bwickenden/PROJ325/Log book Pages/1.jpg

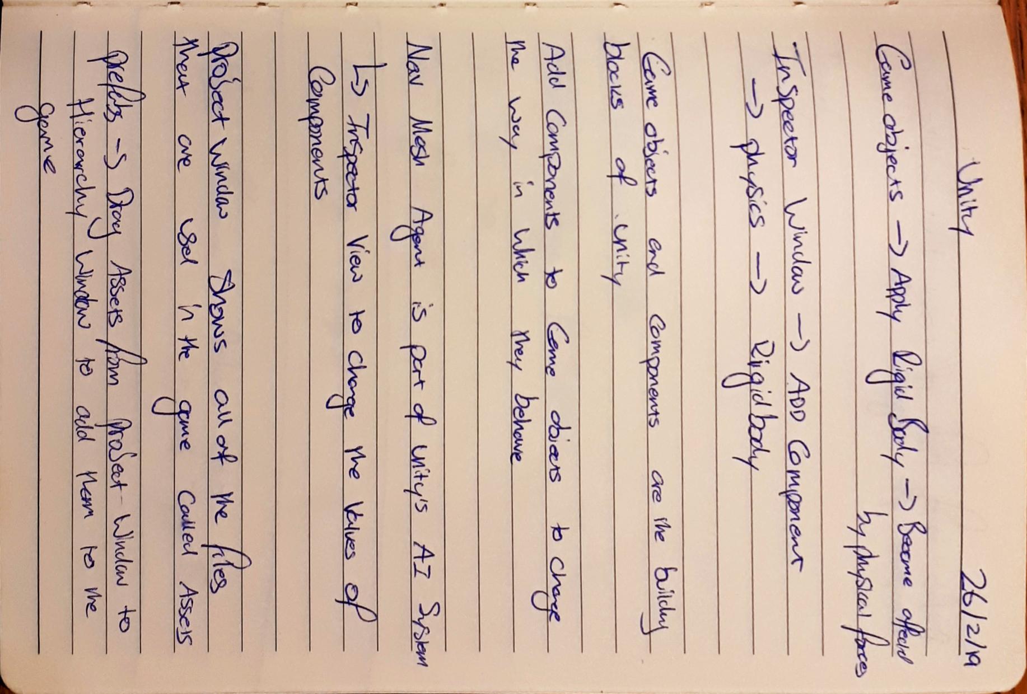
Log book Pages/1.jpg
