bwickenden/PROJ325/Log book Pages/2.jpg

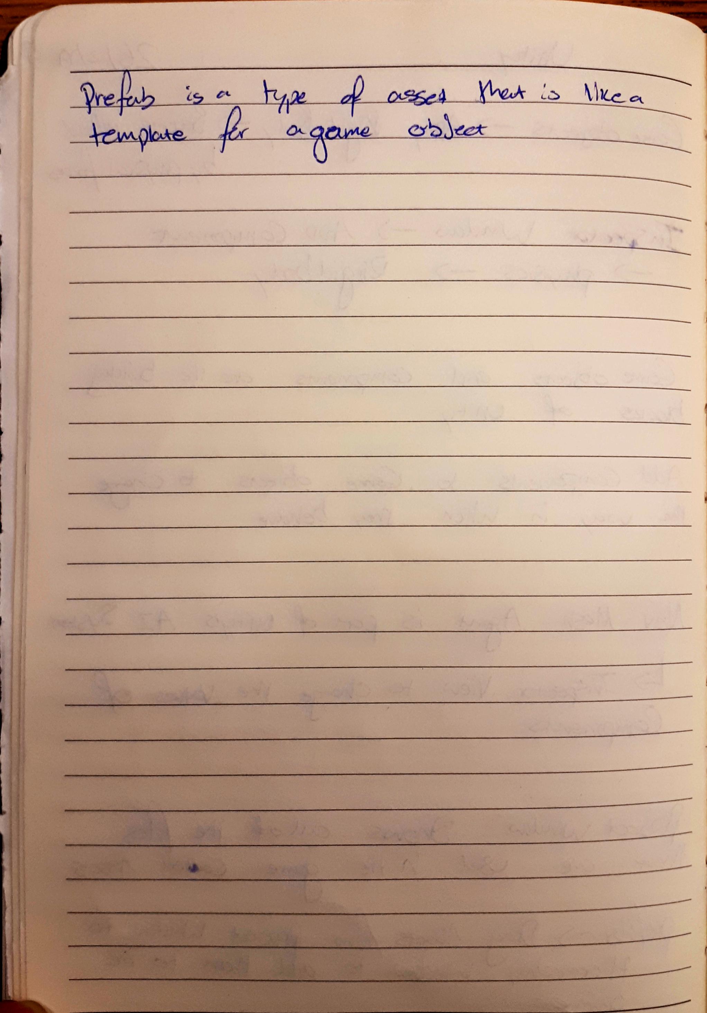
Log book Pages/2.jpg
