bwickenden/PROJ325/Log book Pages/3.jpg

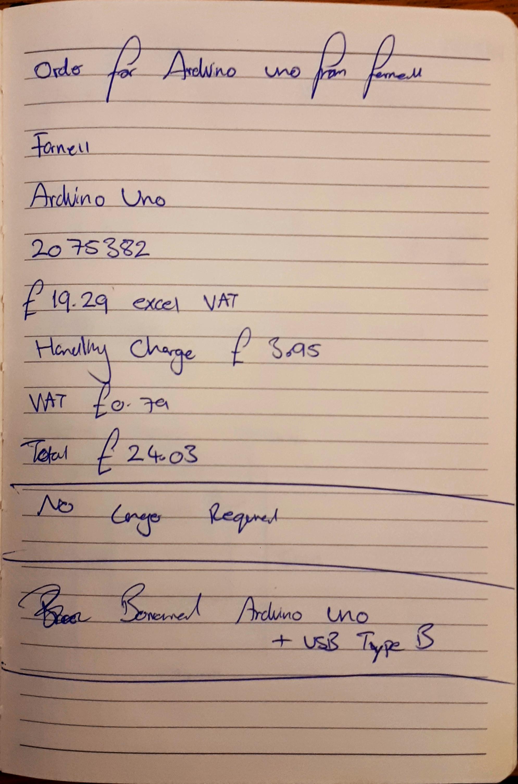
Log book Pages/3.jpg
