bwickenden/PROJ325/Log book Pages/4.jpg

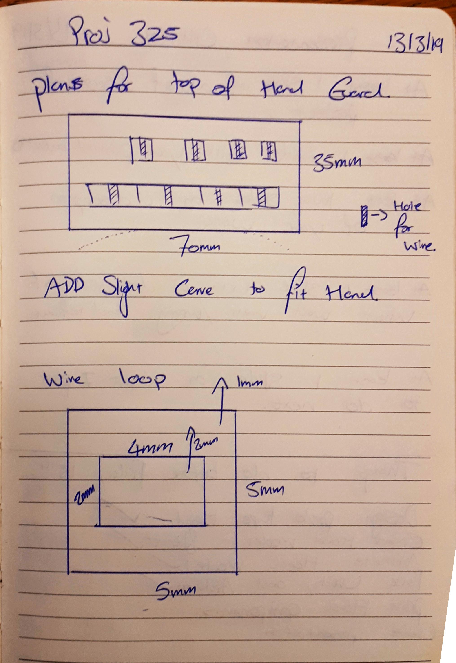
Log book Pages/4.jpg
