bwickenden/PROJ325/Log book Pages/5.jpg

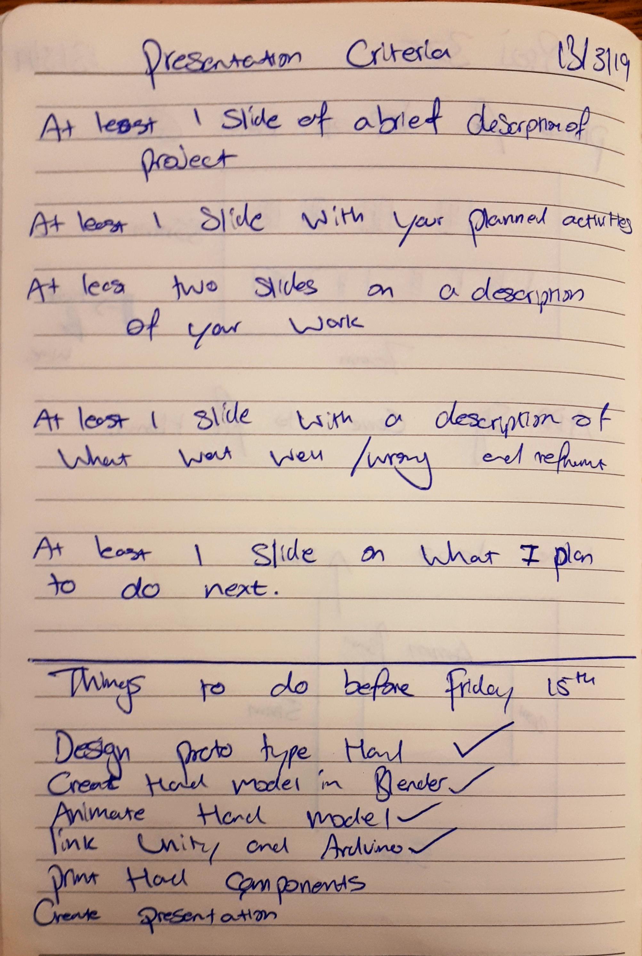
Log book Pages/5.jpg
