bwickenden/PROJ325/Log book Pages/6.jpg

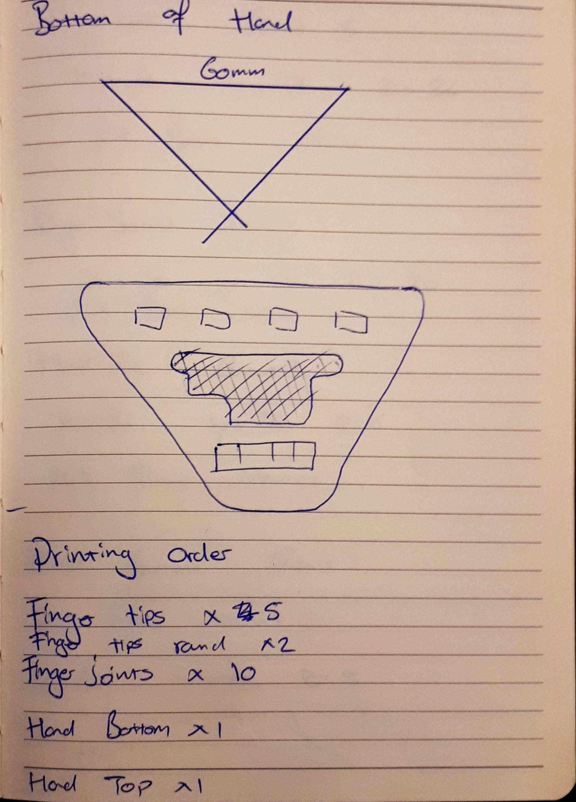
Log book Pages/6.jpg
