bwickenden/PROJ325/Log book Pages/7.jpg

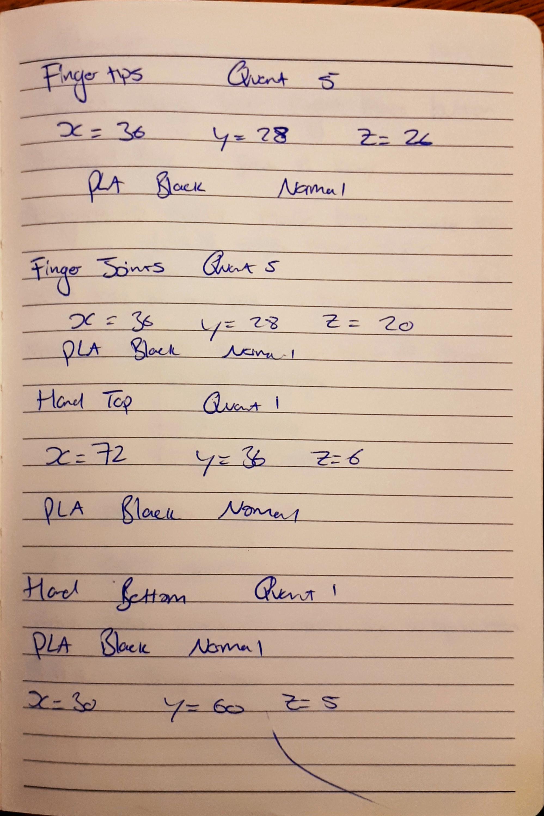
Log book Pages/7.jpg
