bwickenden/PROJ325/Log book Pages/8.jpg

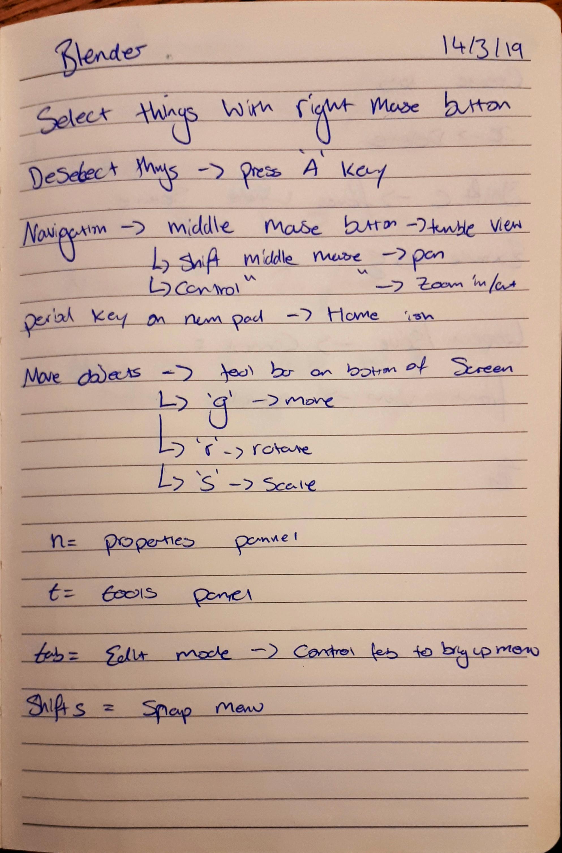
Log book Pages/8.jpg
