bwickenden/PROJ325/Log book Pages/9.jpg

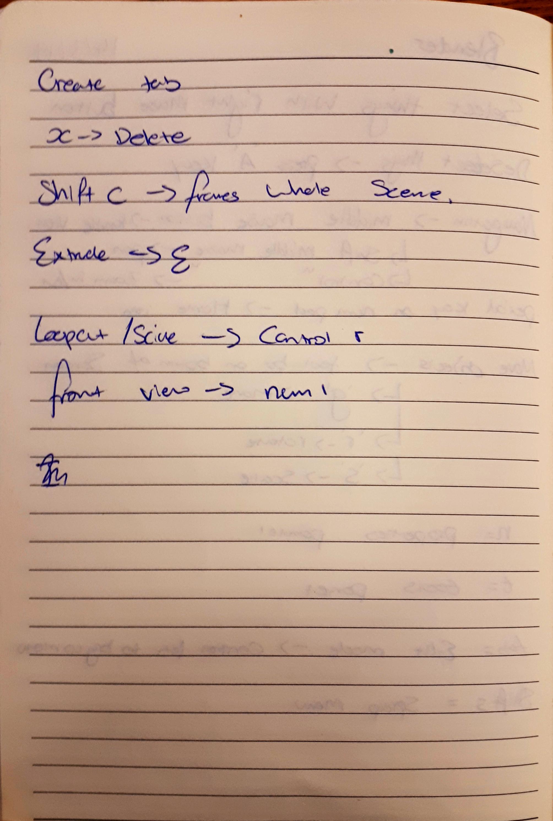
Log book Pages/9.jpg
