bwickenden/PROJ325/Log book Pages/10.jpg

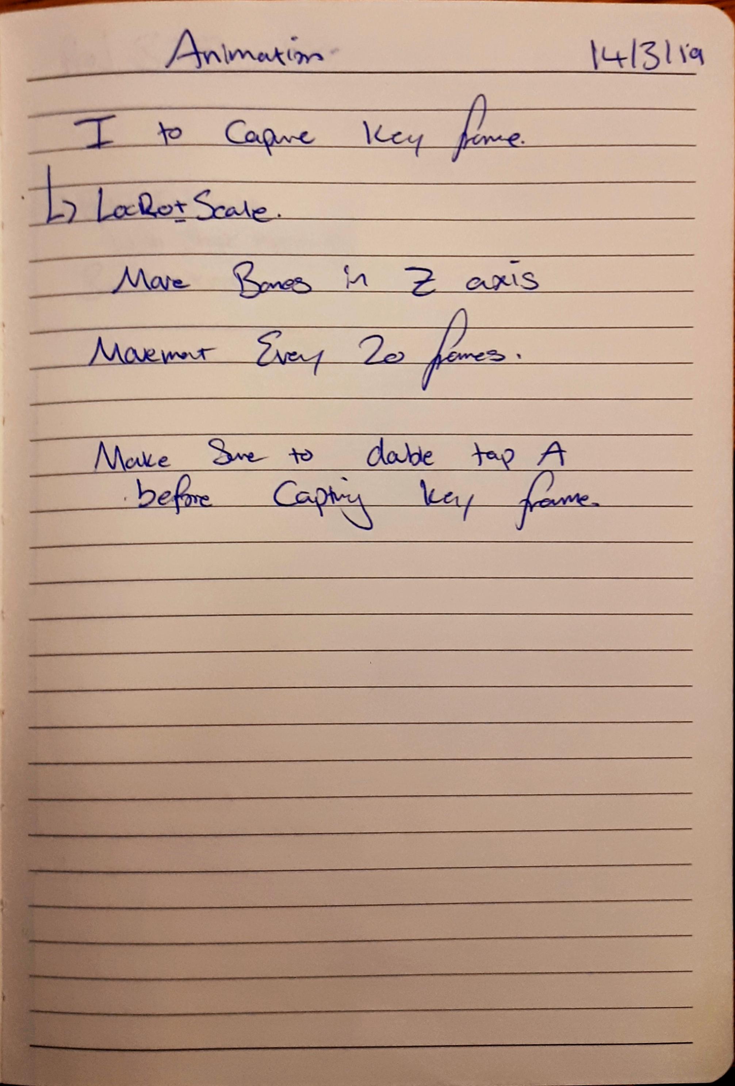
Log book Pages/10.jpg
