bwickenden/PROJ325/Log book Pages/12.jpg

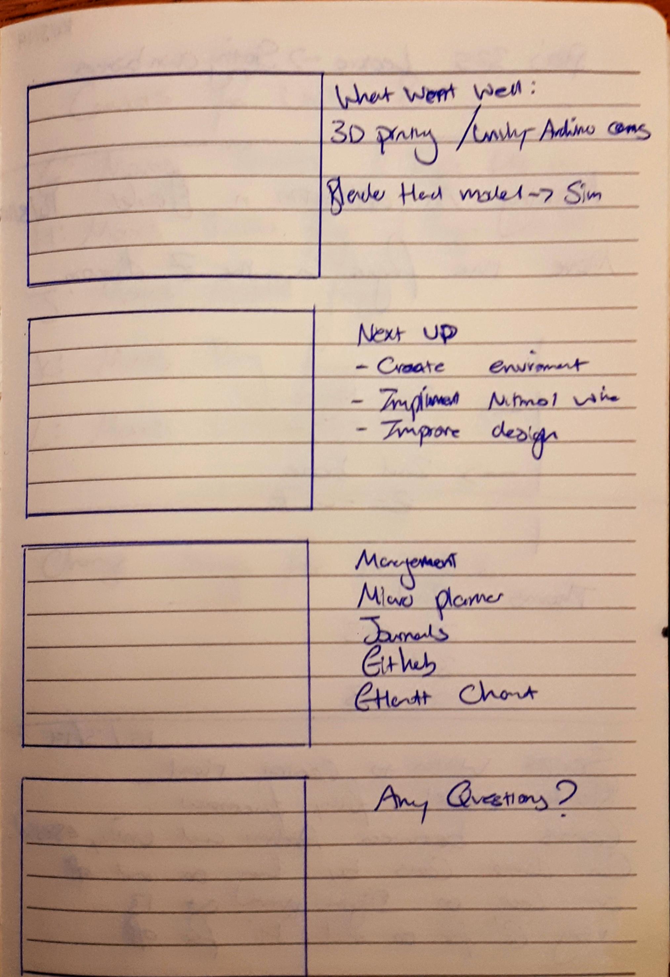
Log book Pages/12.jpg
