bwickenden/PROJ325/Log book Pages/13.jpg

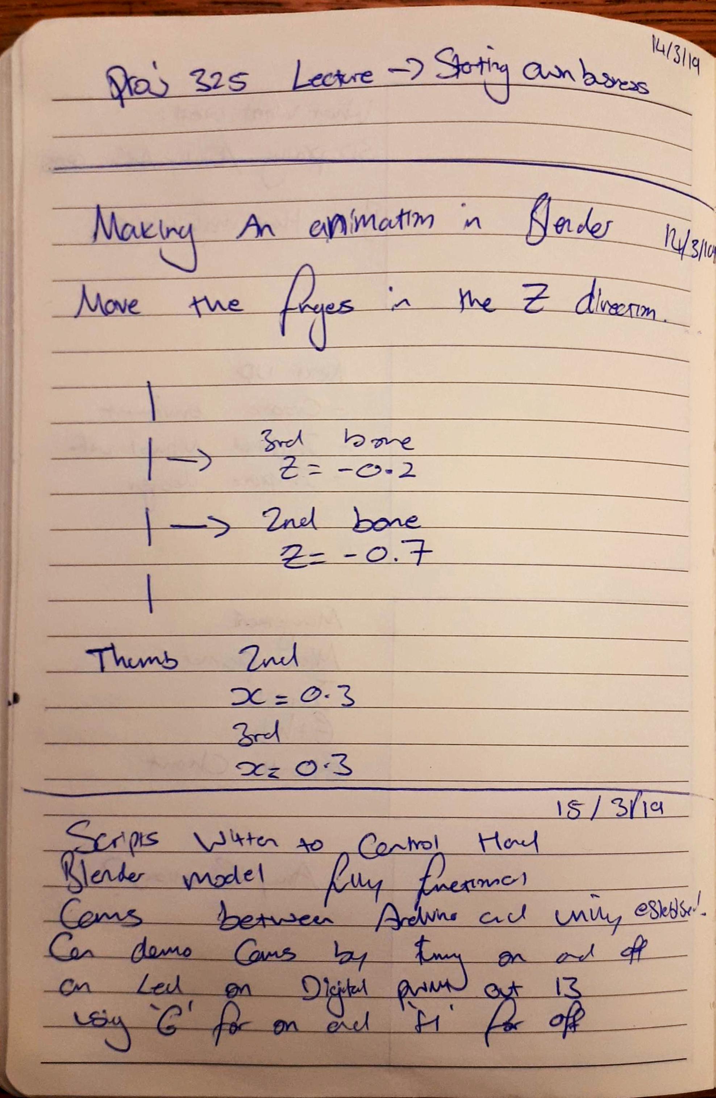
Log book Pages/13.jpg
