bwickenden/PROJ325/Log book Pages/14.jpg

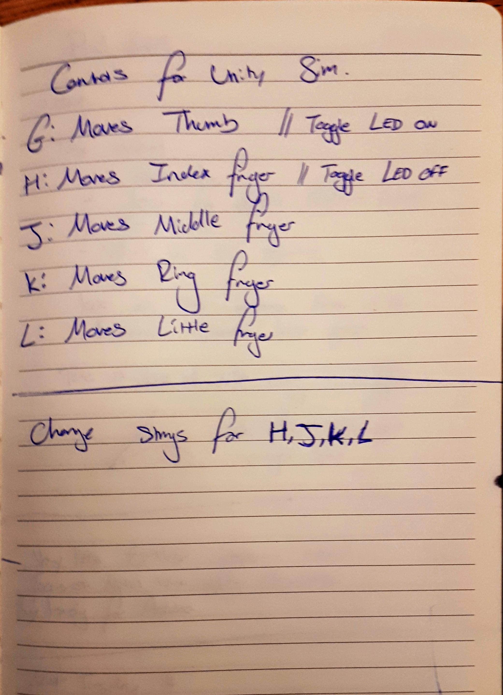
Log book Pages/14.jpg
