bwickenden/PROJ325/Log book Pages/15 (1).jpg

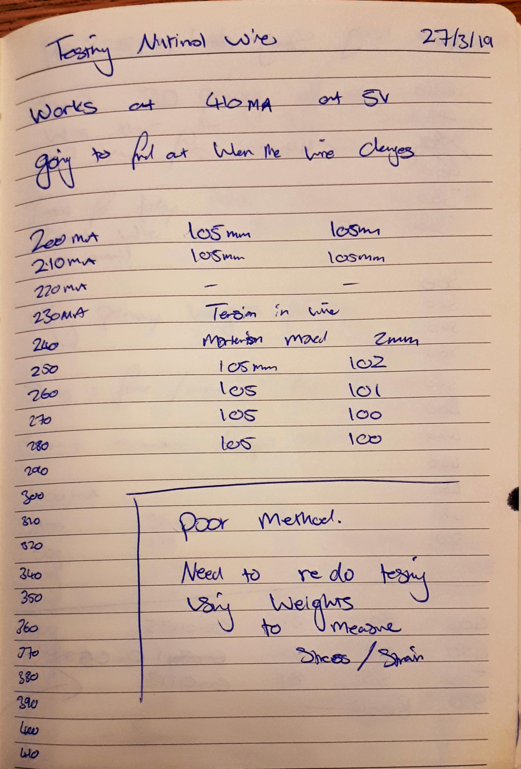
Log book Pages/15 (1).jpg
