bwickenden/PROJ325/Log book Pages/15.jpg

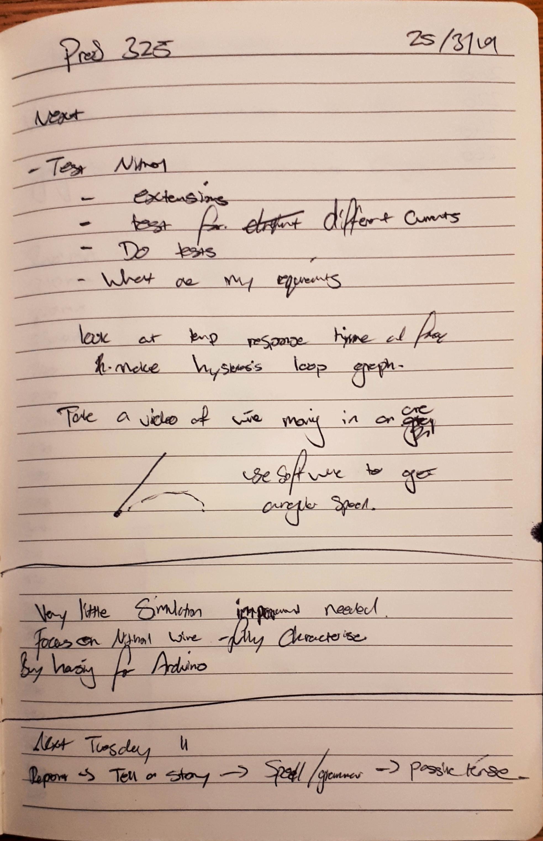
Log book Pages/15.jpg
