bwickenden/PROJ325/Log book Pages/16.jpg

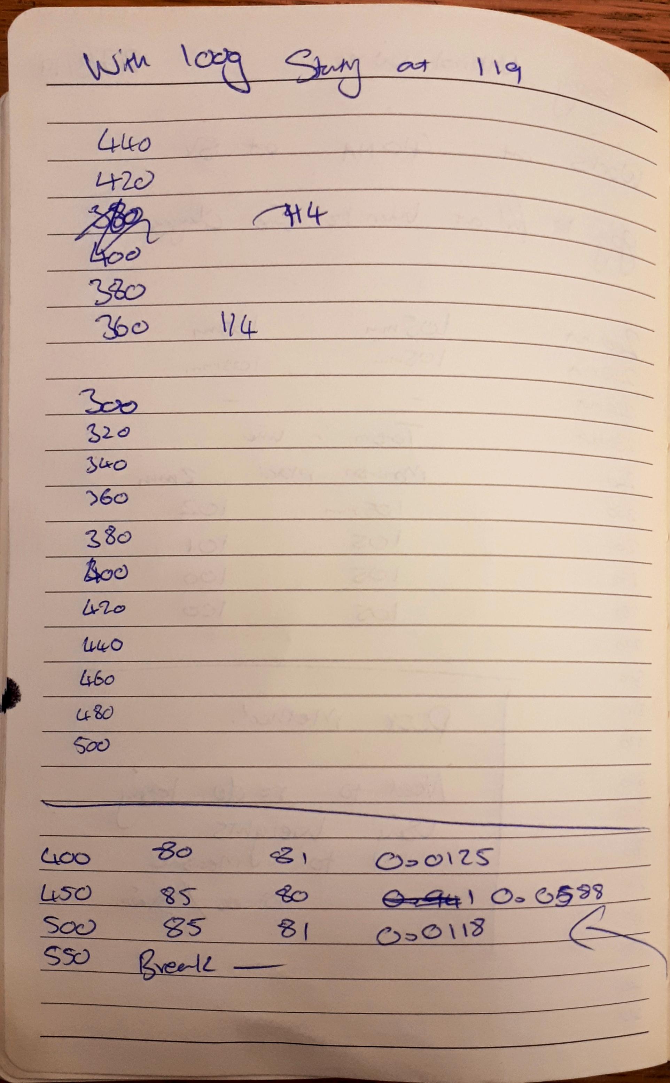
Log book Pages/16.jpg
