bwickenden/PROJ325/Log book Pages/17.jpg

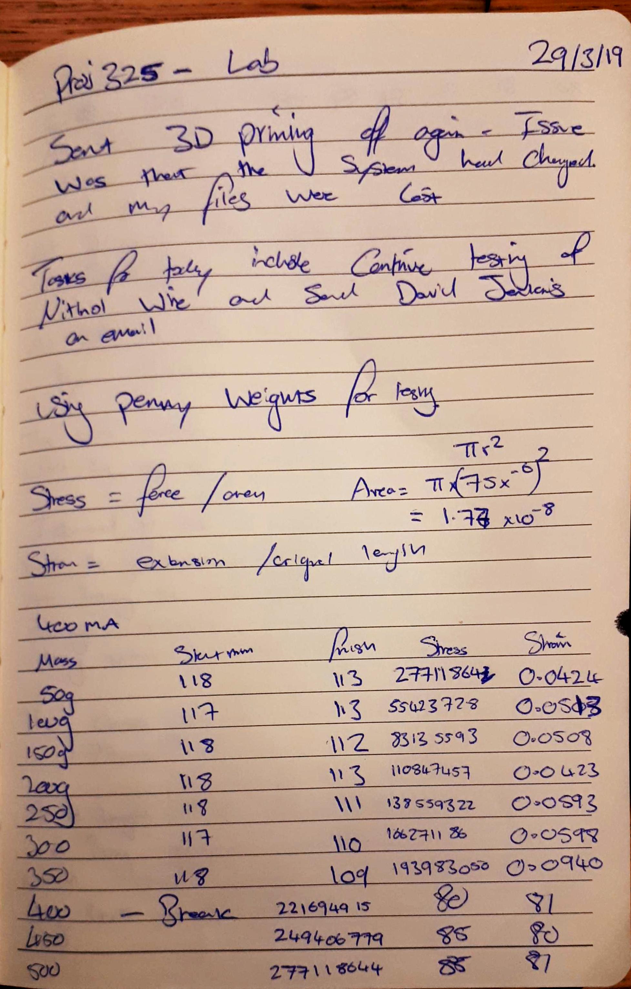
Log book Pages/17.jpg
