bwickenden/PROJ325/Log book Pages/18.jpg

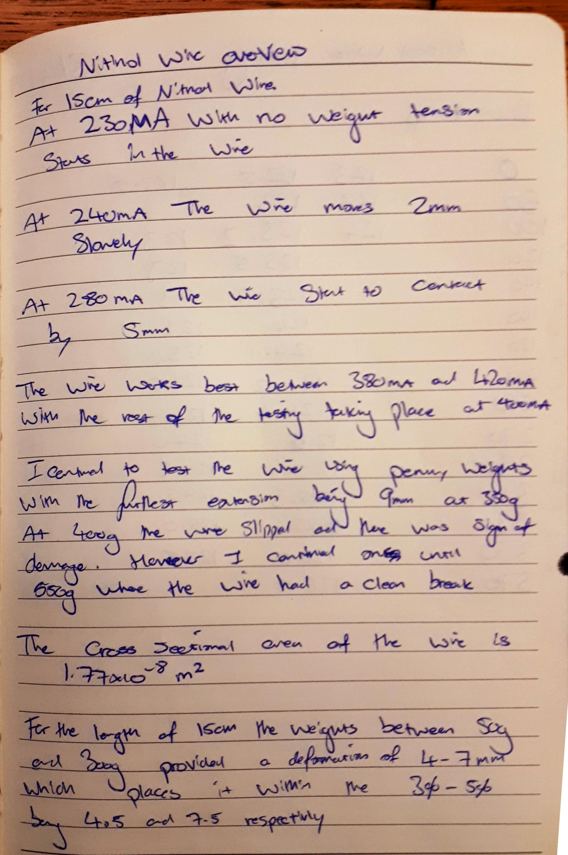
Log book Pages/18.jpg
