bwickenden/PROJ325/Log book Pages/19 (1).jpg

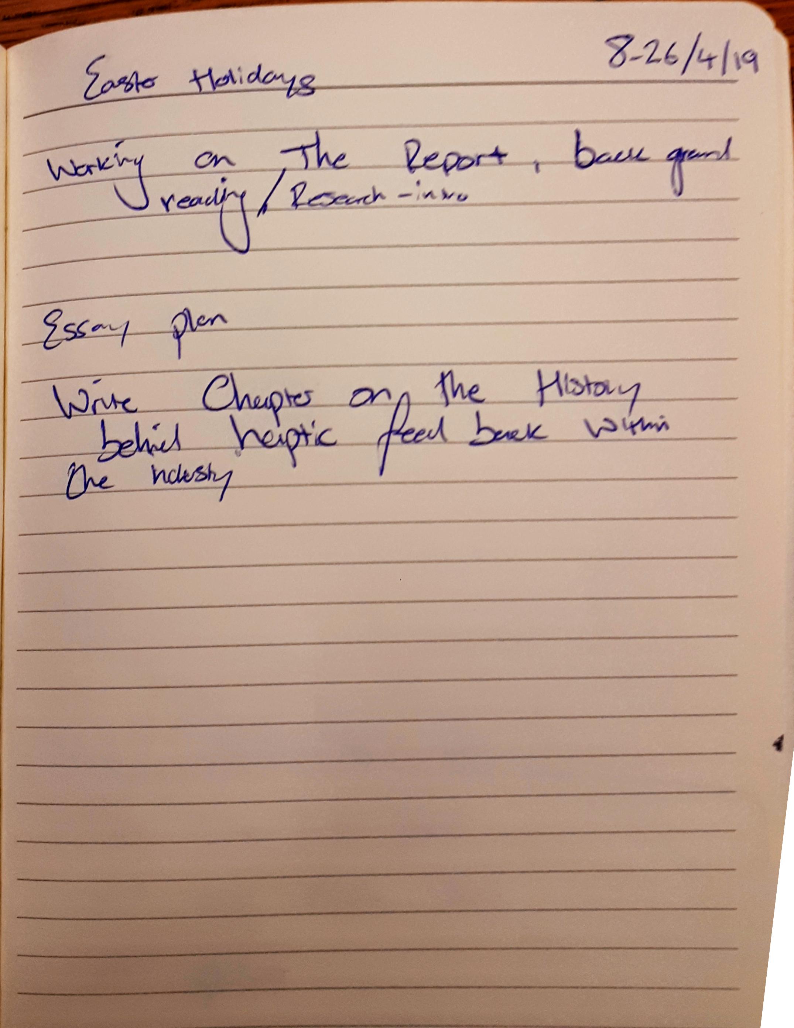
Log book Pages/19 (1).jpg
