bwickenden/PROJ325/Log book Pages/19 (2).jpg

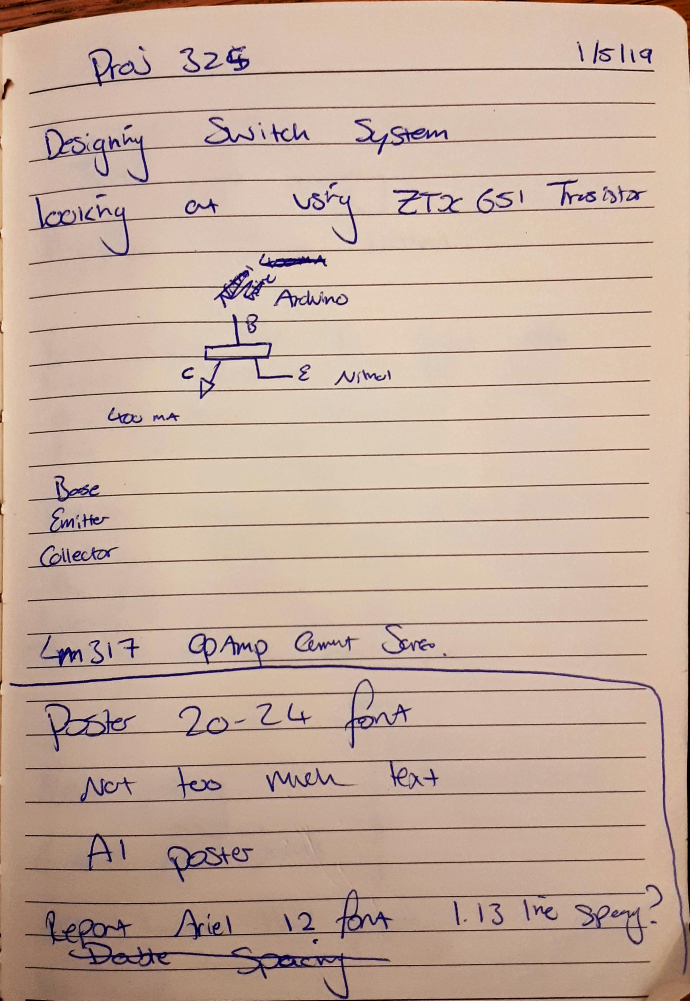
Log book Pages/19 (2).jpg
