bwickenden/PROJ325/Log book Pages/19.jpg

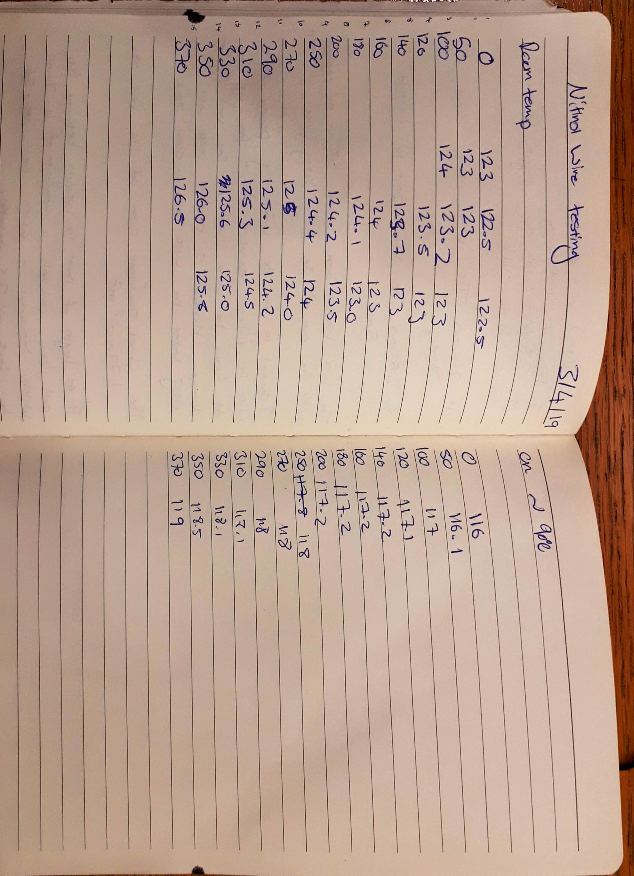
Log book Pages/19.jpg
