bwickenden/PROJ325/Log book Pages/20.jpg

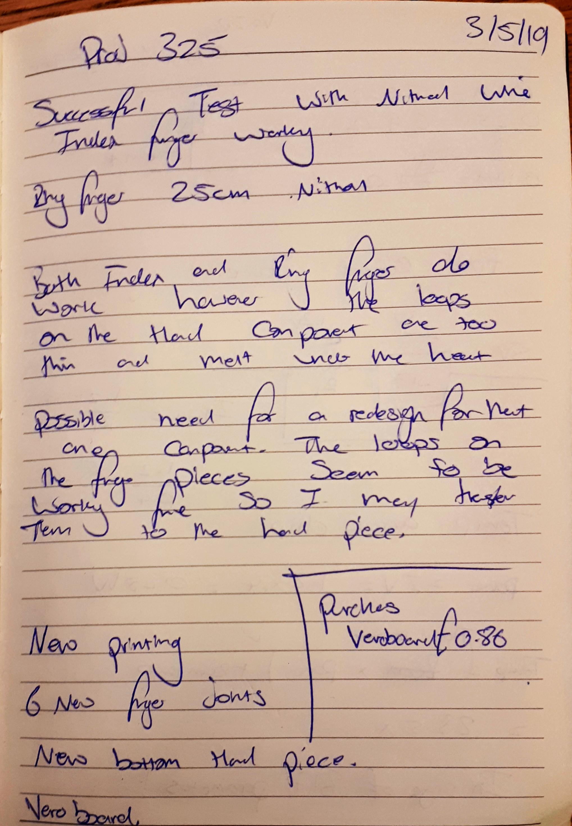
Log book Pages/20.jpg
