bwickenden/PROJ325/Log book Pages/21.jpg

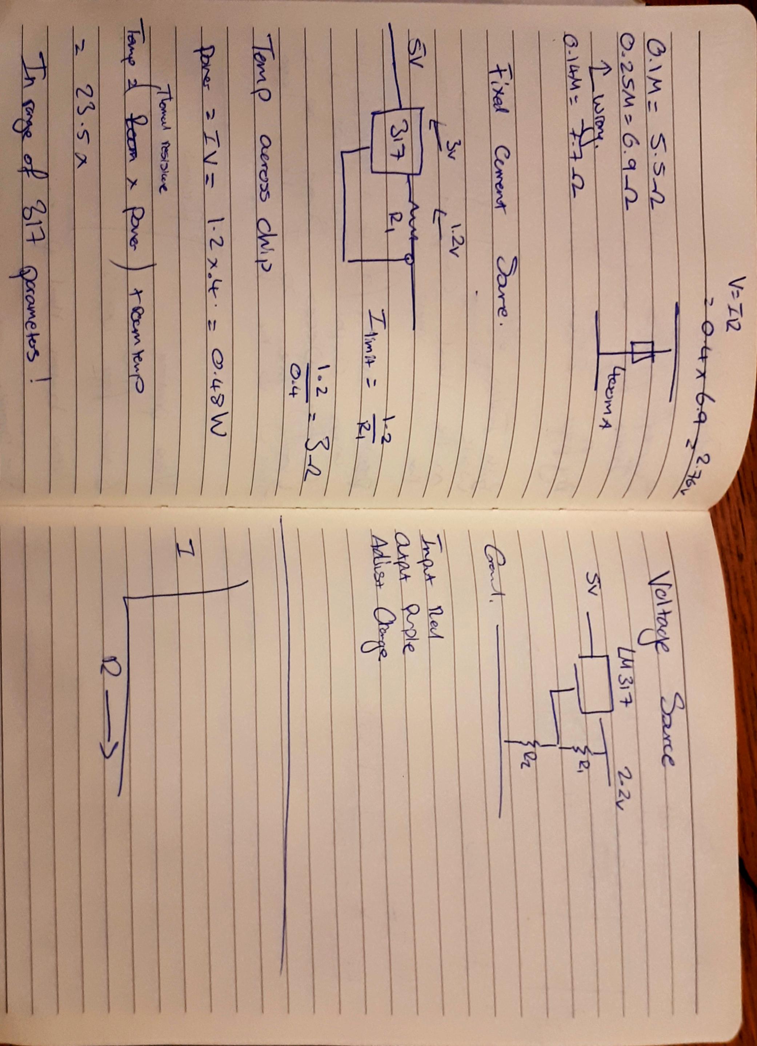
Log book Pages/21.jpg
