bwickenden/PROJ325/Log book Pages/22.jpg

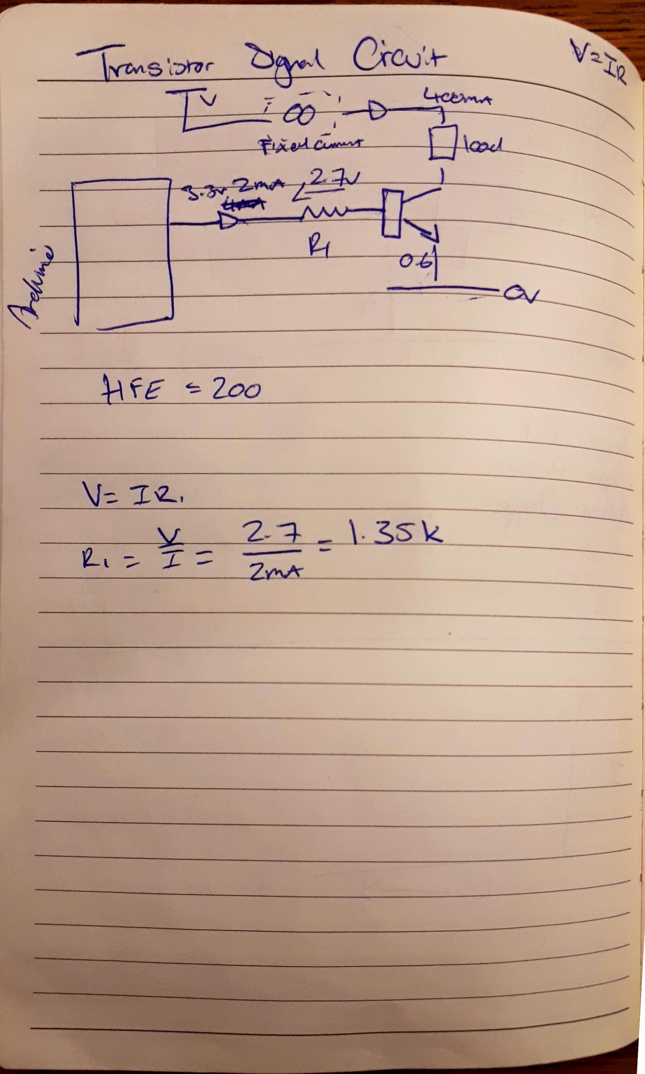
Log book Pages/22.jpg
