bwickenden/PROJ325/Log book Pages/23.jpg

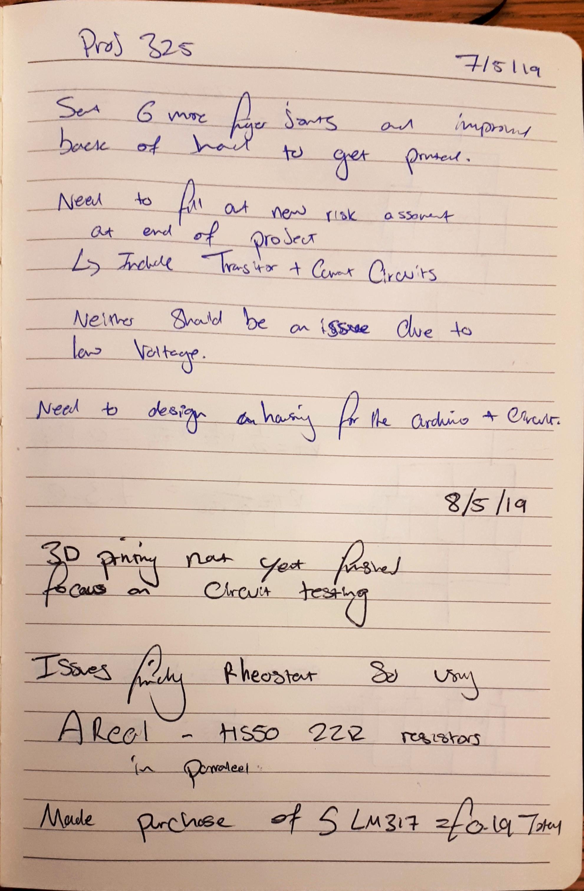
Log book Pages/23.jpg
