bwickenden/PROJ325/Log book Pages/24 (1).jpg

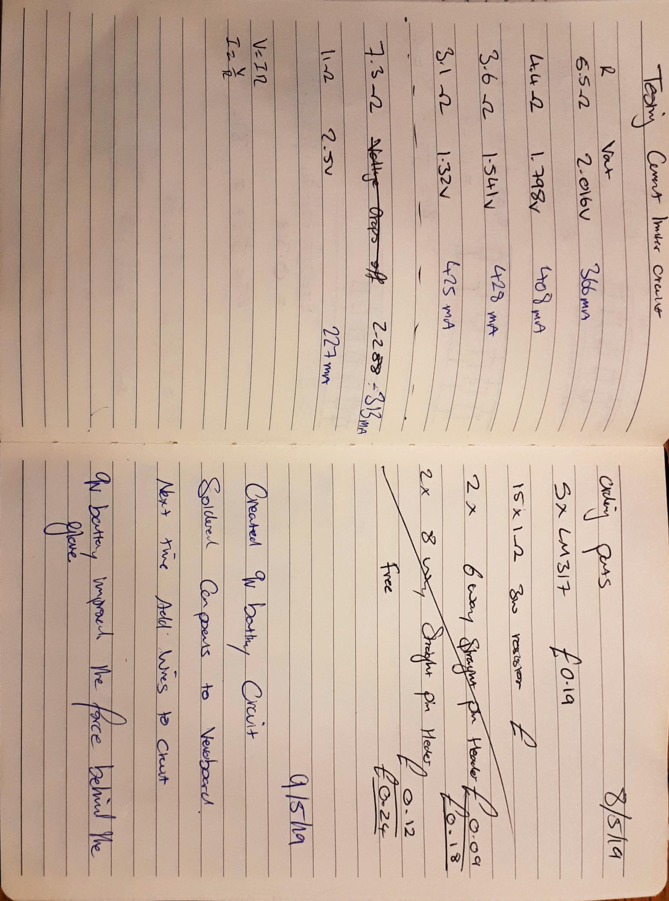
Log book Pages/24 (1).jpg
