bwickenden/PROJ325/Log book Pages/24.jpg

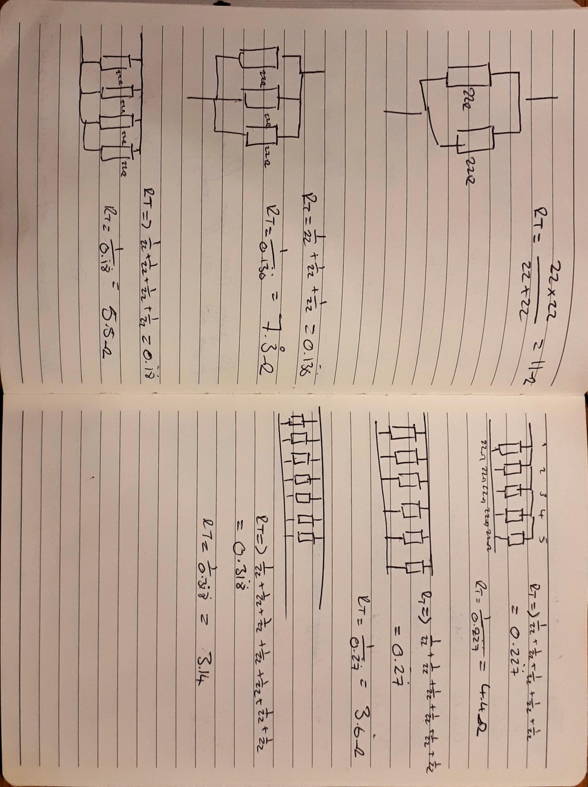
Log book Pages/24.jpg
