bwickenden/PROJ325/Log book Pages/25.jpg

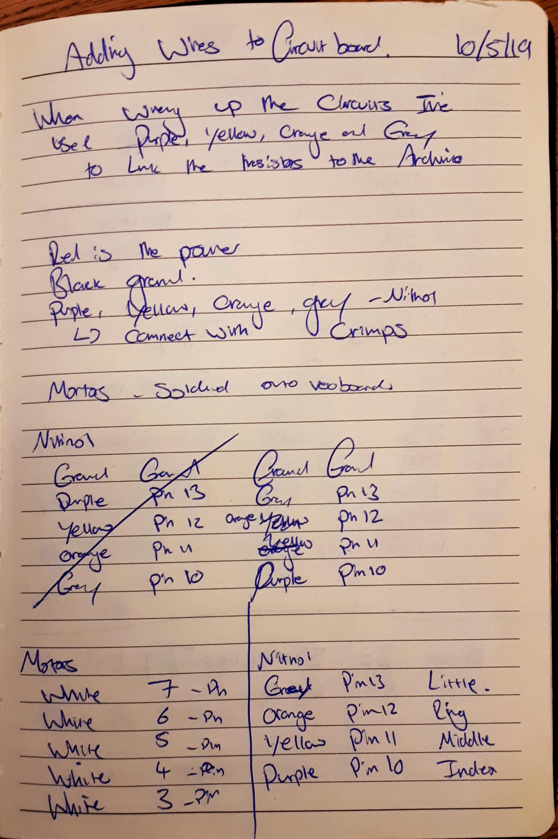
Log book Pages/25.jpg
