bwickenden/PROJ325/Log book Pages/26.jpg

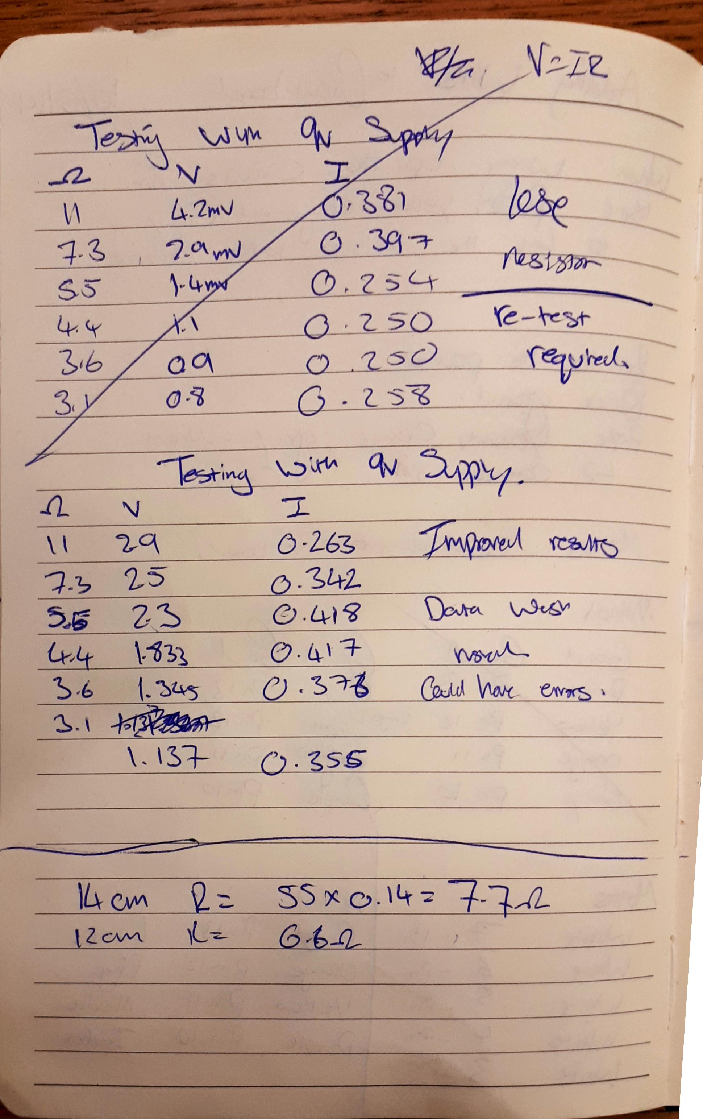
Log book Pages/26.jpg
