bwickenden/PROJ325/Log book Pages/28.jpg

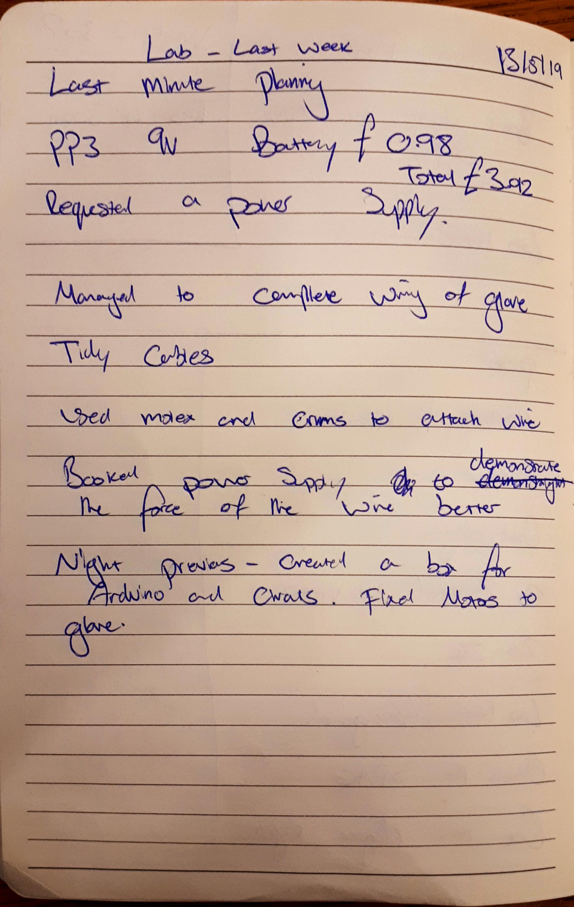
Log book Pages/28.jpg
