bwickenden/PROJ325/Log book Pages/29.jpg

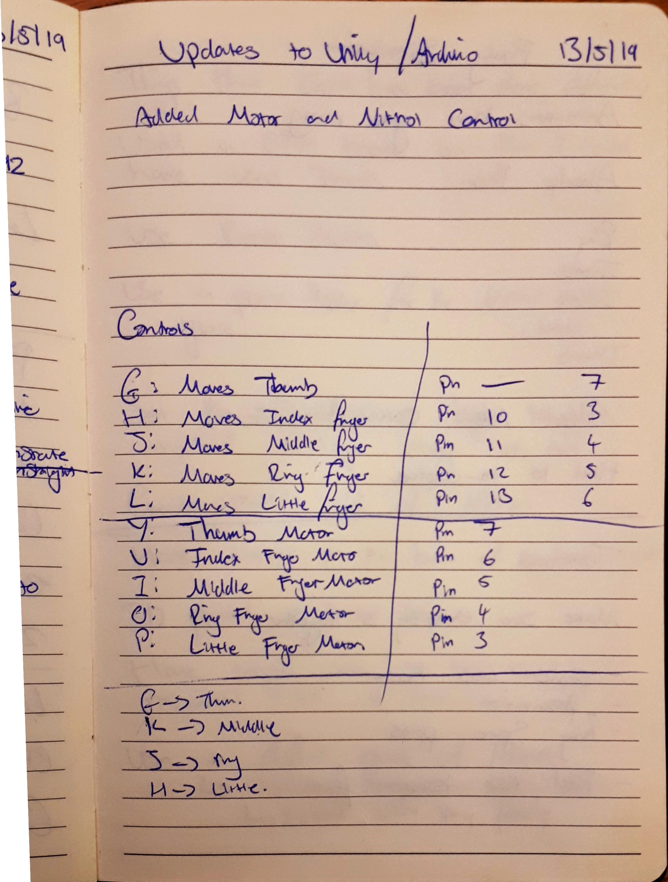
Log book Pages/29.jpg
