bwickenden/PROJ325/Log book Pages/30.jpg

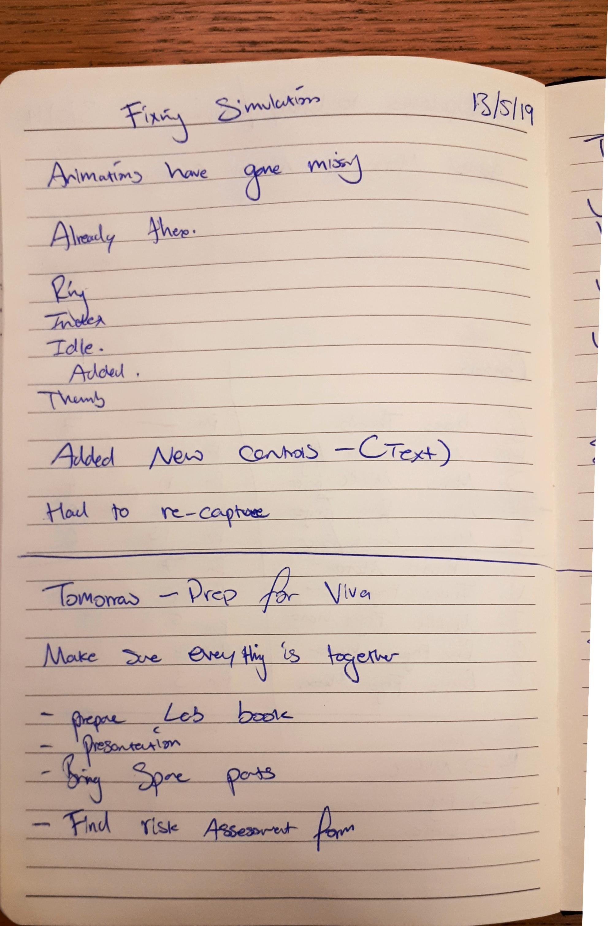
Log book Pages/30.jpg
