bwickenden/PROJ325/Log book Pages/31.jpg

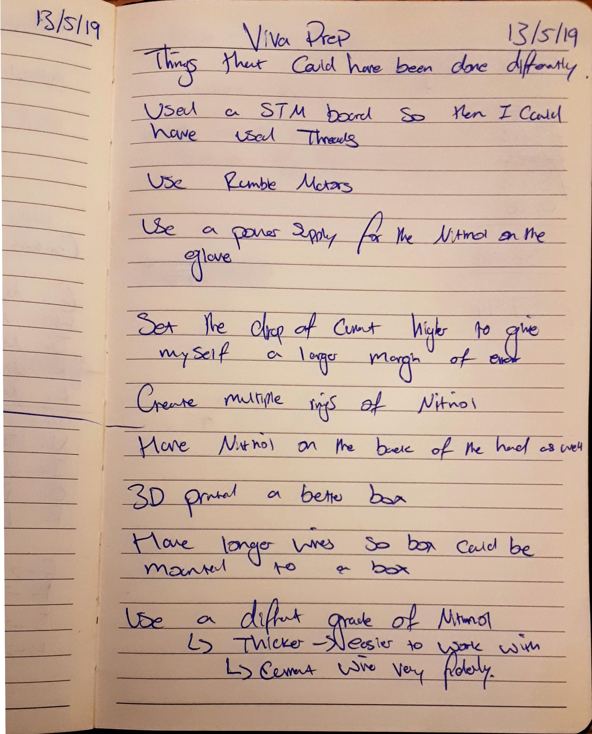
Log book Pages/31.jpg
