bwickenden/PROJ325/Log book Pages/32.jpg

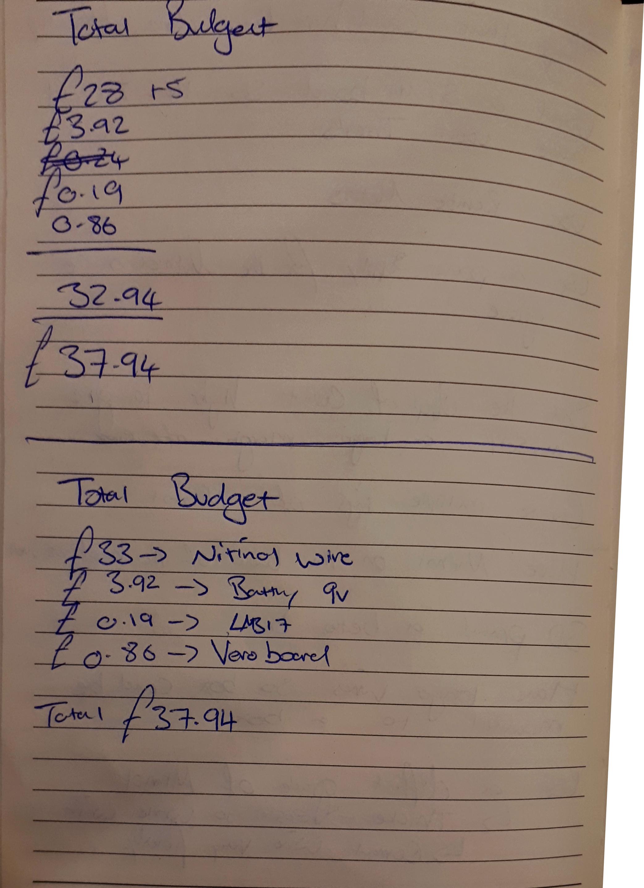
Log book Pages/32.jpg
