bwickenden/PROJ325/Log book Pages/33.jpg

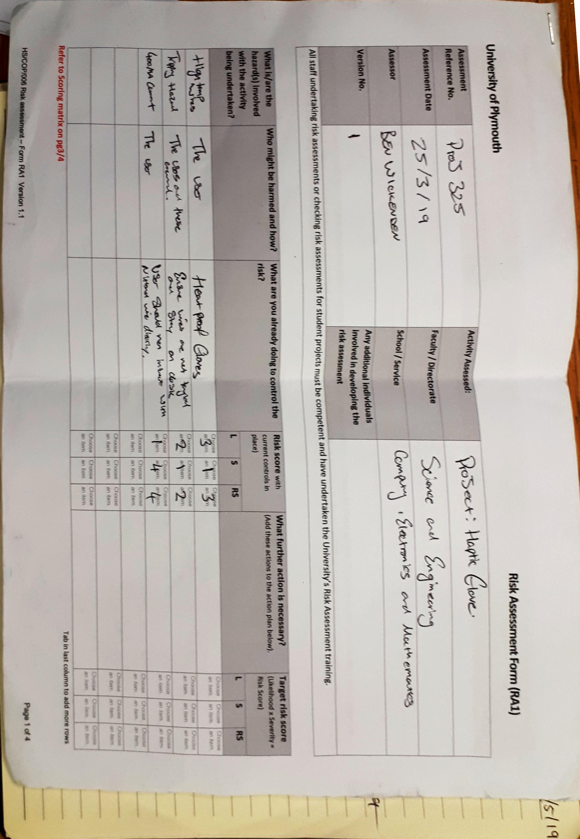
Log book Pages/33.jpg
