bwickenden/PROJ325/Log book Pages/Flexinol.jpg

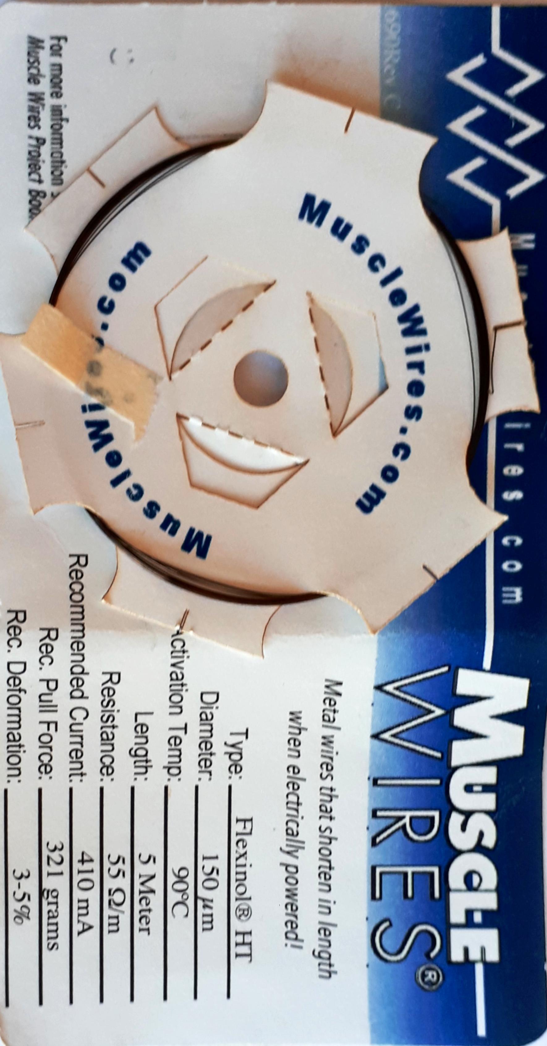
Log book Pages/Flexinol.jpg
