bwickenden/PROJ325/Log book Pages/img001.jpg

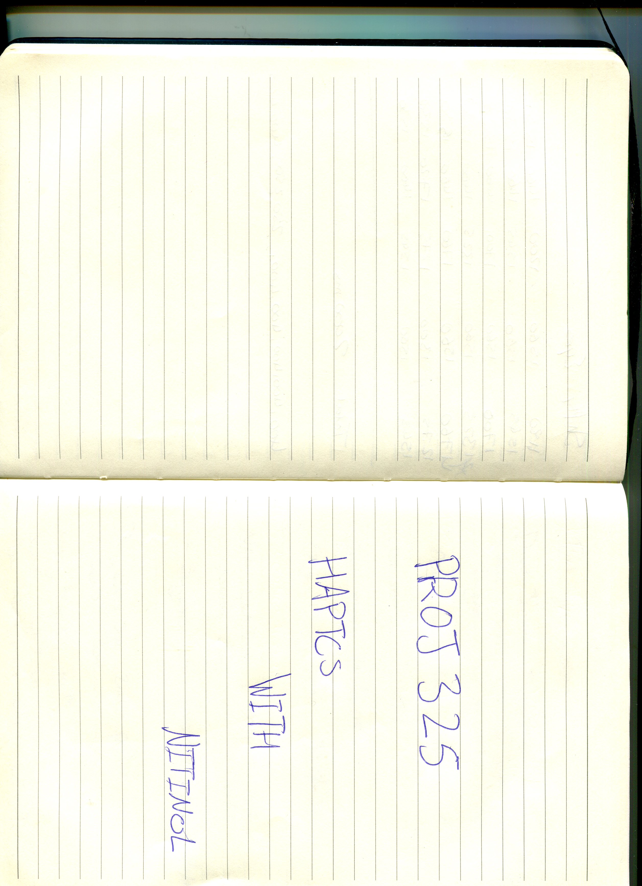
Log book Pages/img001.jpg
