bwickenden/PROJ325/Log book Pages/img002.jpg

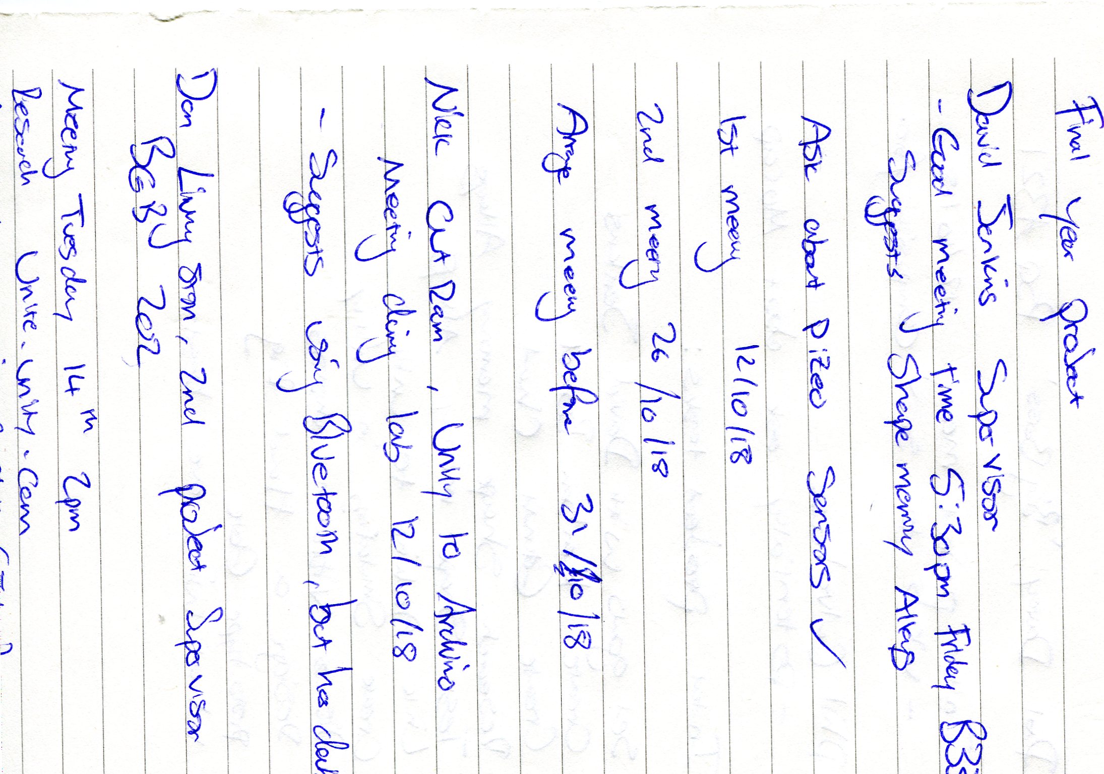
Log book Pages/img002.jpg
