bwickenden/PROJ325/Log book Pages/img003.jpg

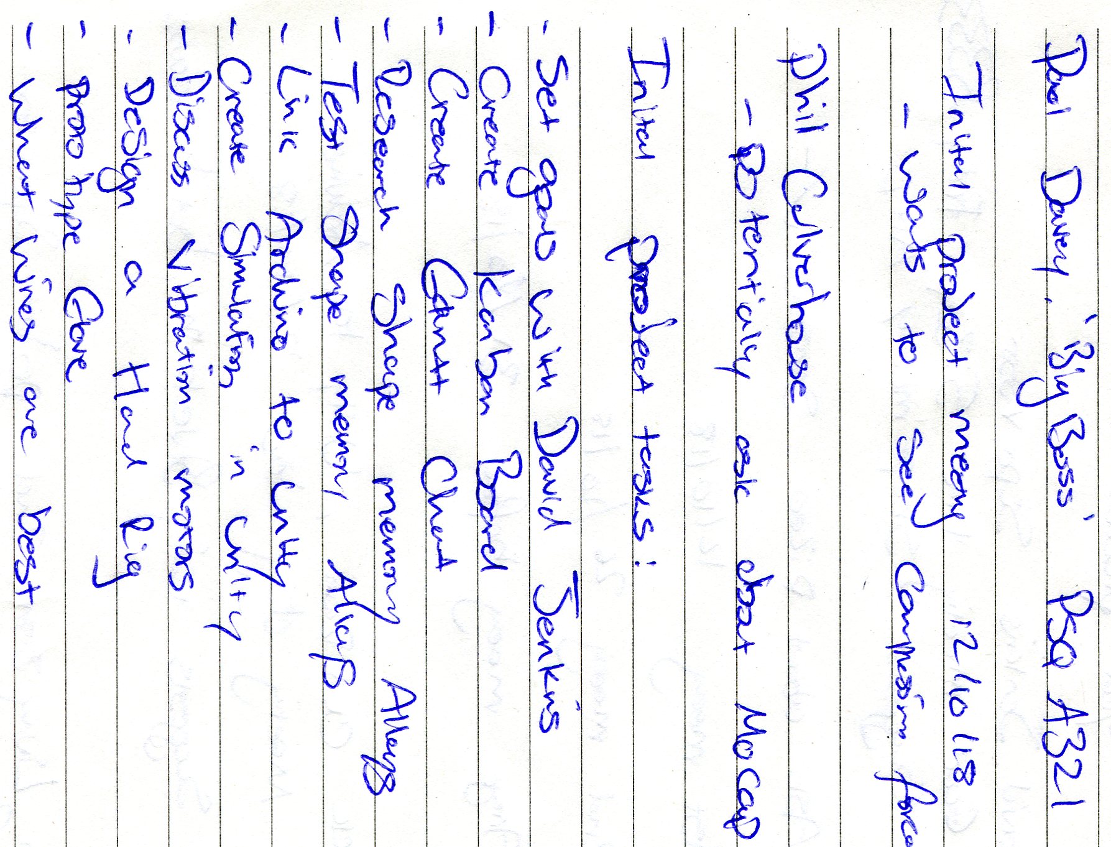
Log book Pages/img003.jpg
