bwickenden/PROJ325/Log book Pages/img004.jpg

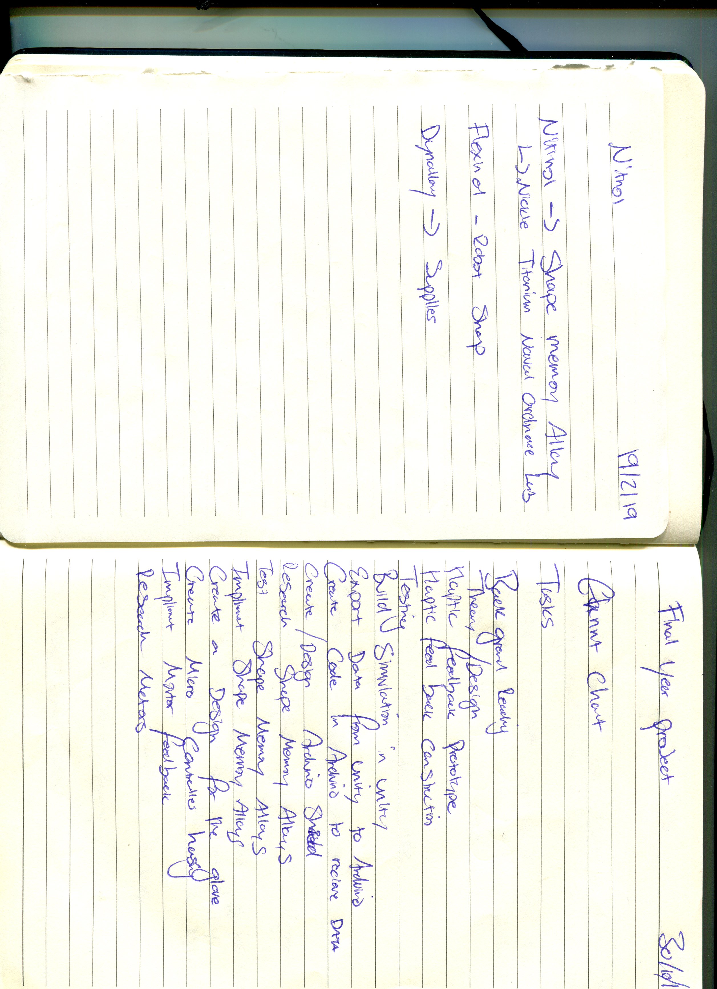
Log book Pages/img004.jpg
