bwickenden/PROJ325/Log book Pages/img005.jpg

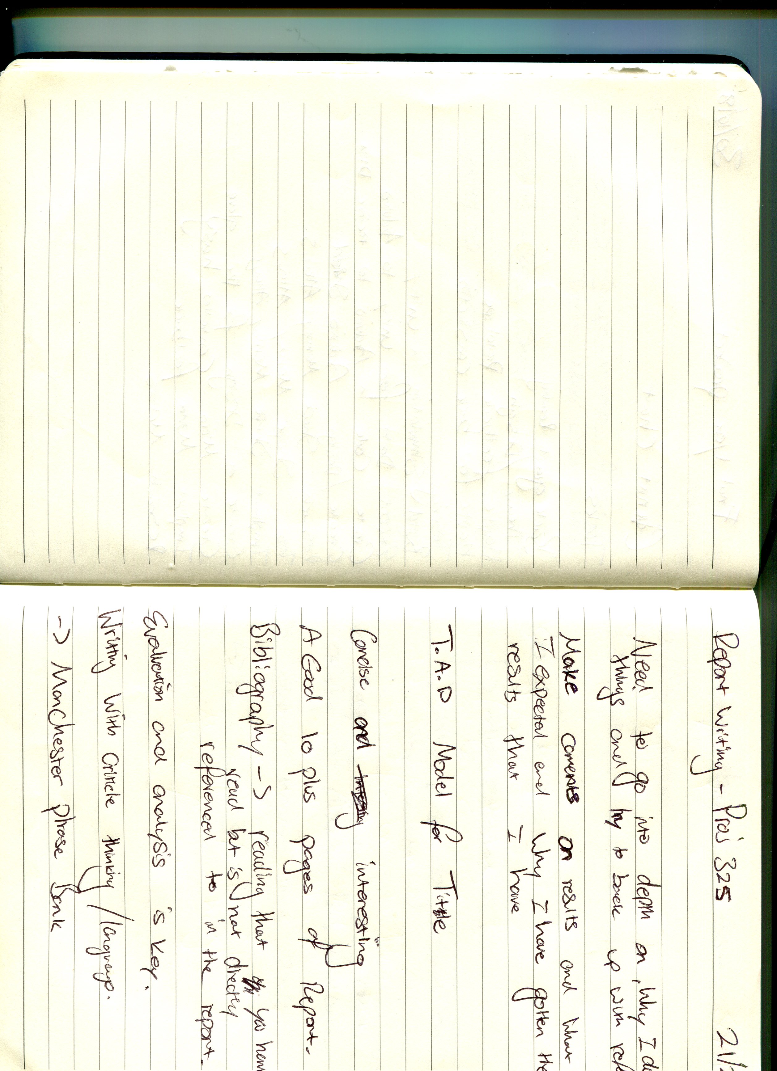
Log book Pages/img005.jpg
